fabiengagne/petg-adhesive-study/media/figures/specimen-panel-d-opposed-pair.tiff

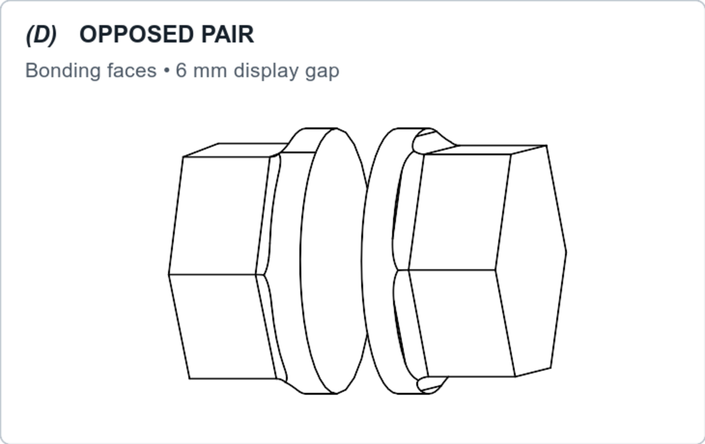
media/figures/specimen-panel-d-opposed-pair.tiff
