fabiengagne/petg-adhesive-study/media/photos/12702.jpg

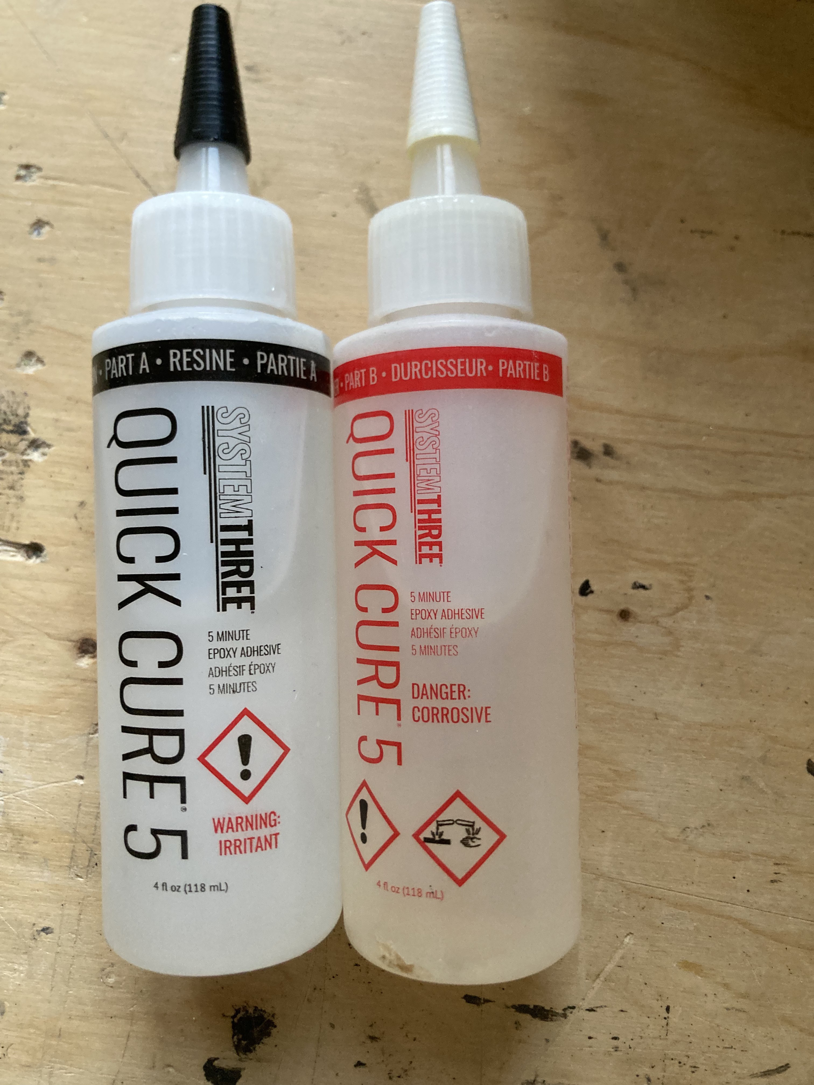
media/photos/12702.jpg
