fabiengagne/petg-adhesive-study/media/photos/12703.jpg

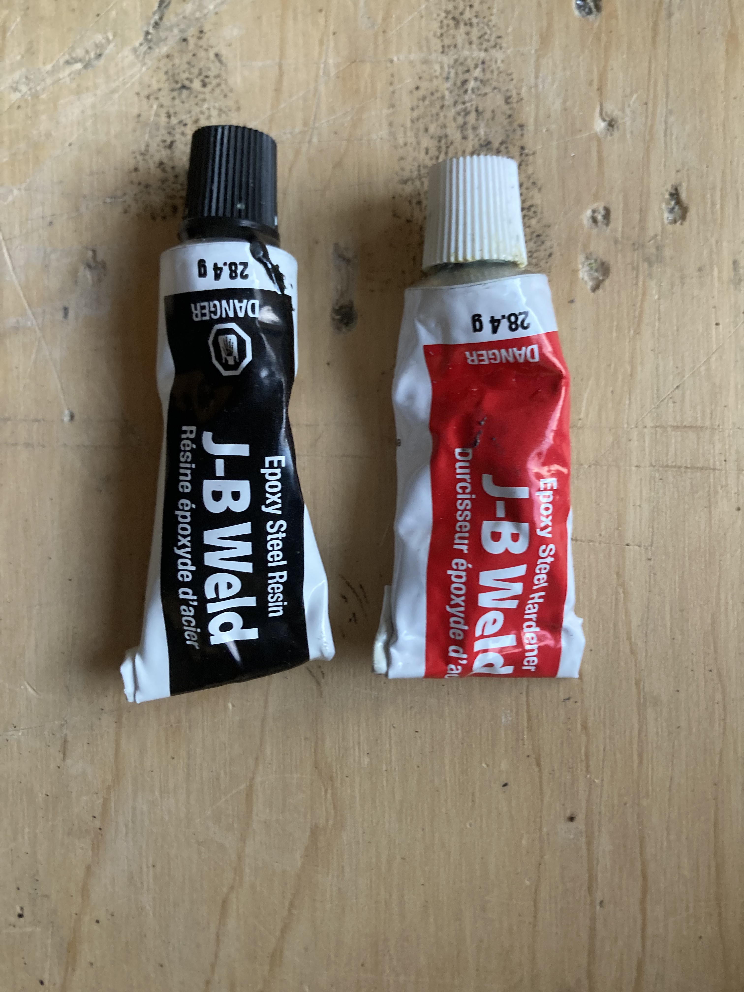
media/photos/12703.jpg
