fabiengagne/petg-adhesive-study/media/photos/12704.jpg

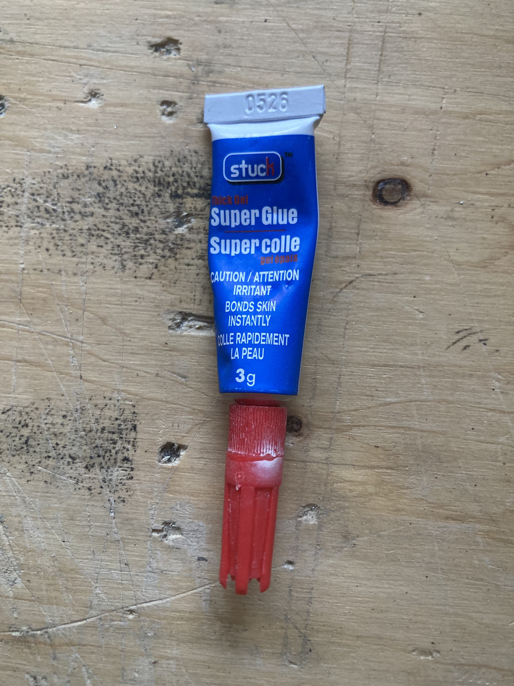
media/photos/12704.jpg
