fabiengagne/petg-adhesive-study/media/photos/12705.jpg

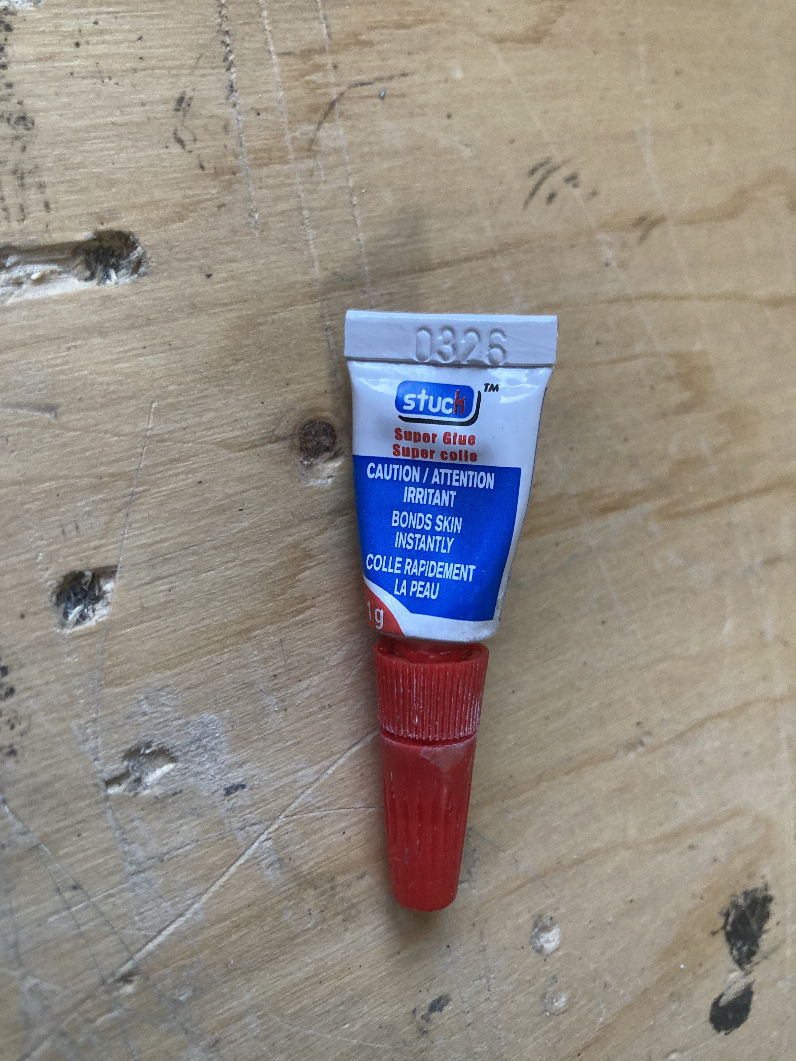
media/photos/12705.jpg
