fabiengagne/petg-adhesive-study/media/photos/12706.jpg

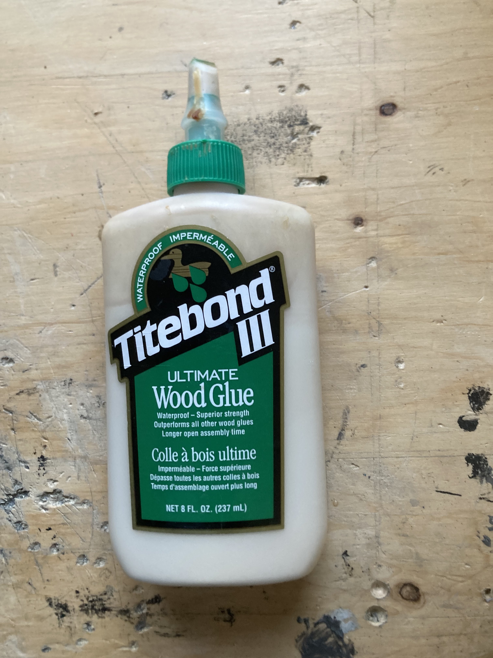
media/photos/12706.jpg
