fabiengagne/petg-adhesive-study/media/photos/12707.jpg

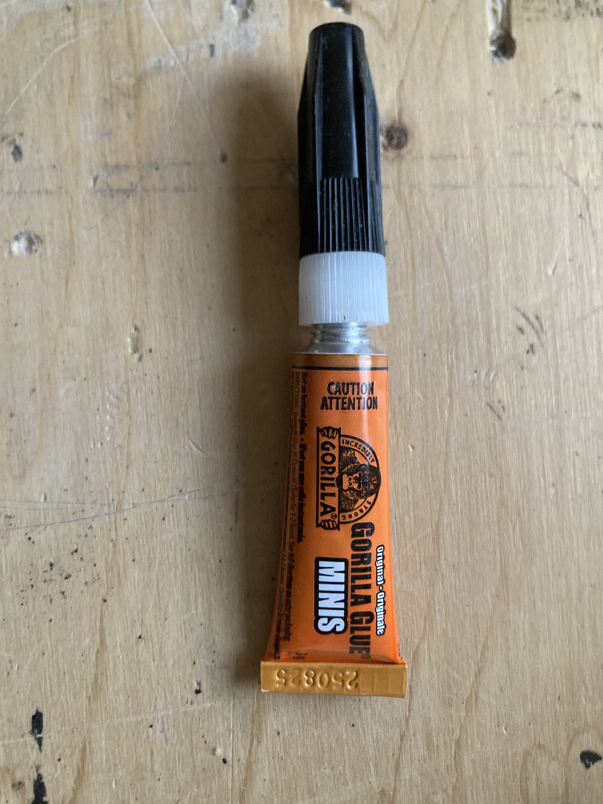
media/photos/12707.jpg
