fabiengagne/petg-adhesive-study/media/photos/12708.jpg

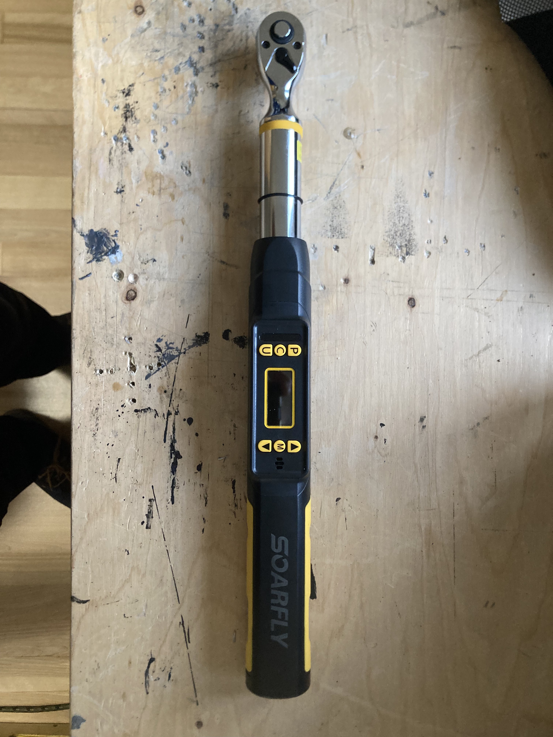
media/photos/12708.jpg
