fabiengagne/petg-adhesive-study/media/photos/12709.jpg

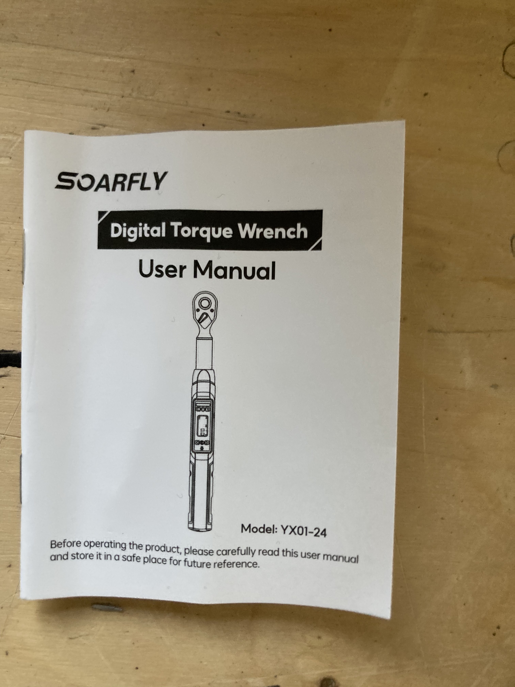
media/photos/12709.jpg
