fabiengagne/petg-adhesive-study/media/photos/12710.jpg

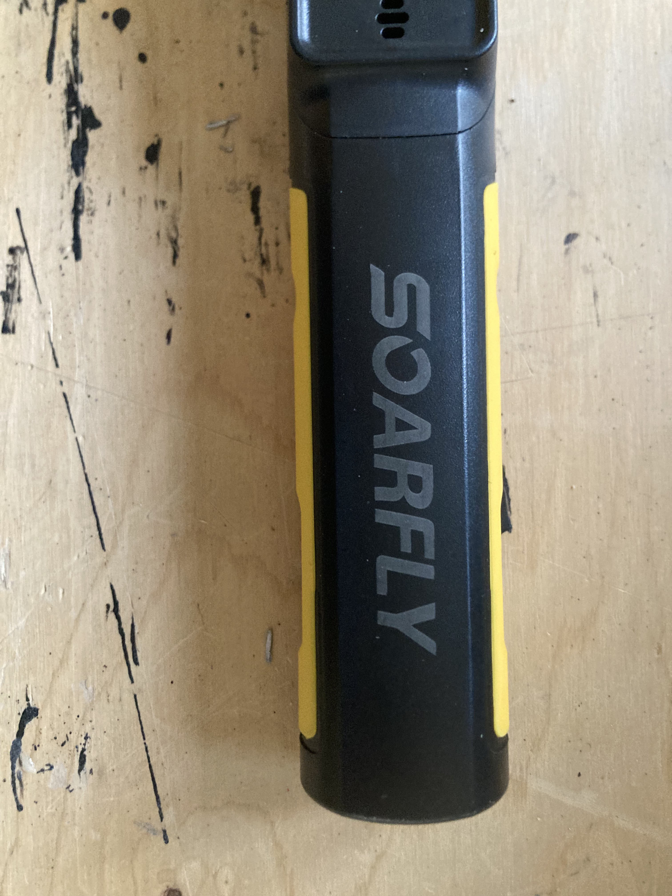
media/photos/12710.jpg
