fabiengagne/petg-adhesive-study/media/photos/petg-filament-lot.jpeg

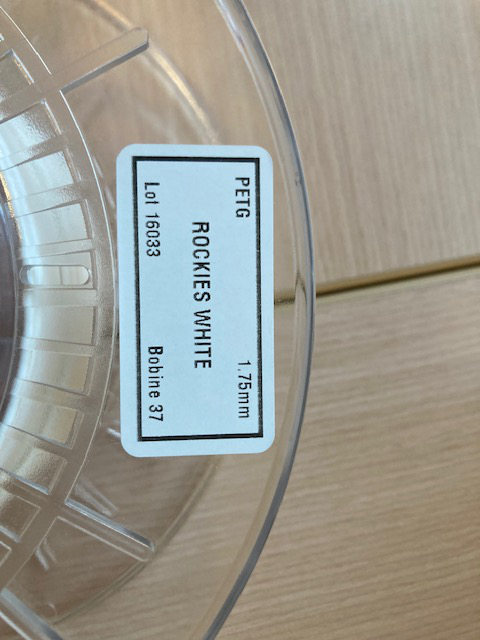
media/photos/petg-filament-lot.jpeg
