fabiengagne/petg-adhesive-study/media/photos/prusaslicer-version.jpeg

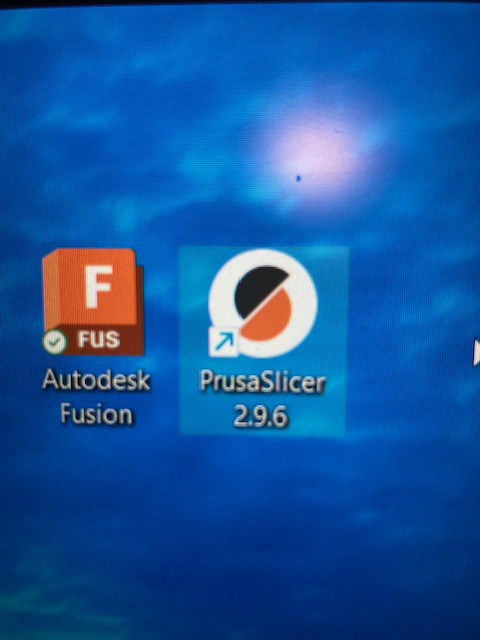
media/photos/prusaslicer-version.jpeg
