fabiengagne/petg-adhesive-study/media/photos/torque-wrench-serial.jpeg

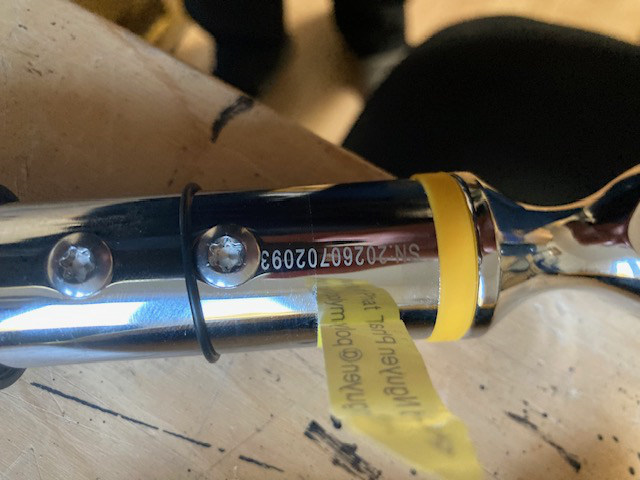
media/photos/torque-wrench-serial.jpeg
